badbooger/Enterprise-D-lighting-effects/enterprise documentation/Warp_Core/images/1a5ce3c3165c4e38cc38278a2bccba72_preview_featured.jpg

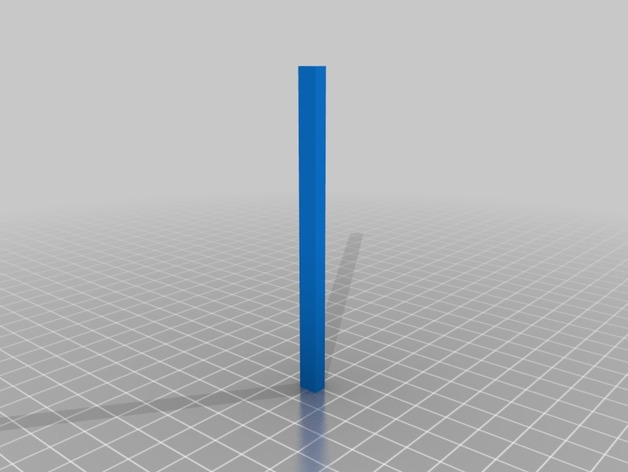
enterprise documentation/Warp_Core/images/1a5ce3c3165c4e38cc38278a2bccba72_preview_featured.jpg
