badbooger/Enterprise-D-lighting-effects/enterprise documentation/Warp_Core/images/2f82c1093543009acfd2d8a2ed61bc1e_preview_featured.jpg

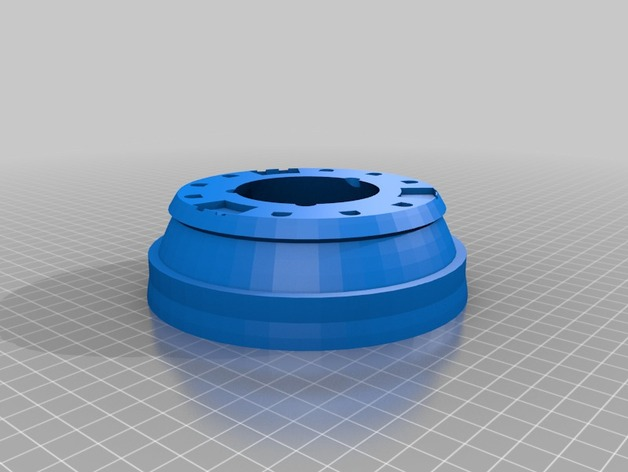
enterprise documentation/Warp_Core/images/2f82c1093543009acfd2d8a2ed61bc1e_preview_featured.jpg
