badbooger/Enterprise-D-lighting-effects/enterprise documentation/Warp_Core/images/4c698710a184a8409cffa17cd85fdf24_preview_featured.jpg

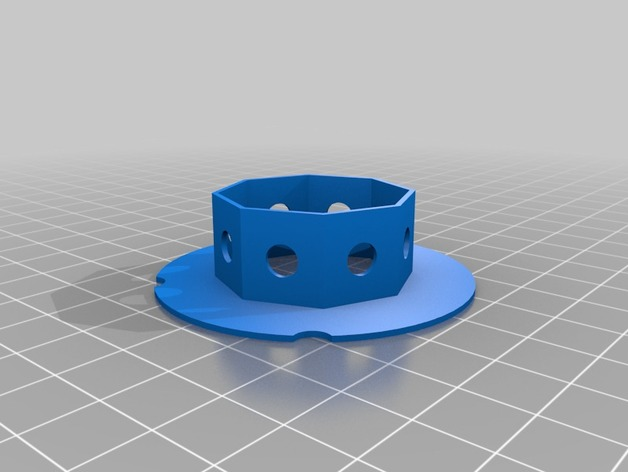
enterprise documentation/Warp_Core/images/4c698710a184a8409cffa17cd85fdf24_preview_featured.jpg
