badbooger/Enterprise-D-lighting-effects/enterprise documentation/Warp_Core/images/5cc91b3e02f9a6b76a1f7cbd91c5c1b0_preview_featured.jpg

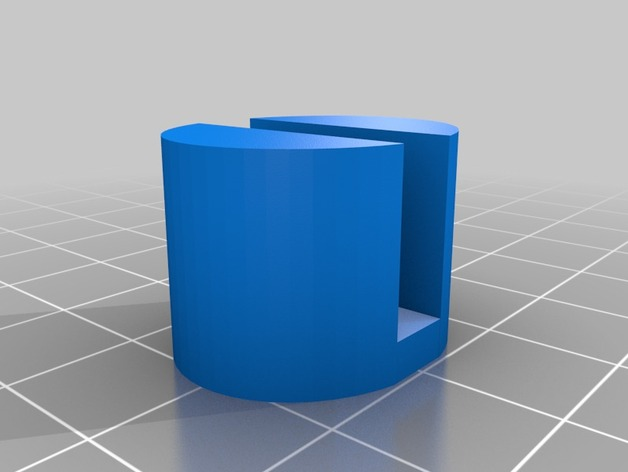
enterprise documentation/Warp_Core/images/5cc91b3e02f9a6b76a1f7cbd91c5c1b0_preview_featured.jpg
