badbooger/Enterprise-D-lighting-effects/enterprise documentation/Warp_Core/images/5dc4bd88d3200d5c8fcbe13b5229334e_preview_featured.jpg

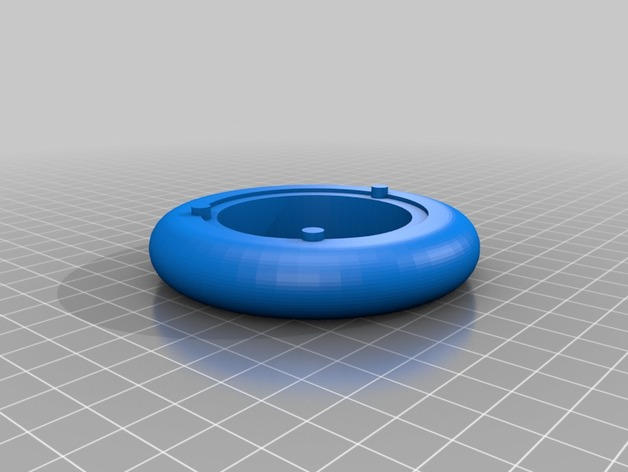
enterprise documentation/Warp_Core/images/5dc4bd88d3200d5c8fcbe13b5229334e_preview_featured.jpg
