badbooger/Enterprise-D-lighting-effects/enterprise documentation/Warp_Core/images/051f70c2b24fe83be3616cc0c08b6ad3_preview_featured.jpg

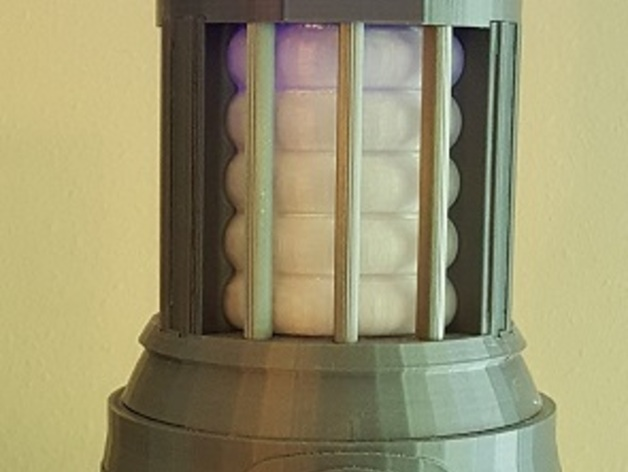
enterprise documentation/Warp_Core/images/051f70c2b24fe83be3616cc0c08b6ad3_preview_featured.jpg
