badbooger/Enterprise-D-lighting-effects/enterprise documentation/Warp_Core/images/58fbbf431e4570eb2abc4635ba671e66_preview_featured.jpg

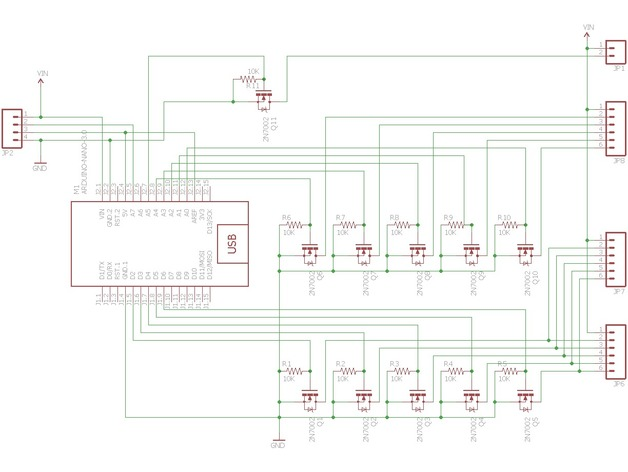
enterprise documentation/Warp_Core/images/58fbbf431e4570eb2abc4635ba671e66_preview_featured.jpg
