badbooger/Enterprise-D-lighting-effects/enterprise documentation/Warp_Core/images/5356e7dd109f7f2495ff2d7921a1a03d_preview_featured.jpg

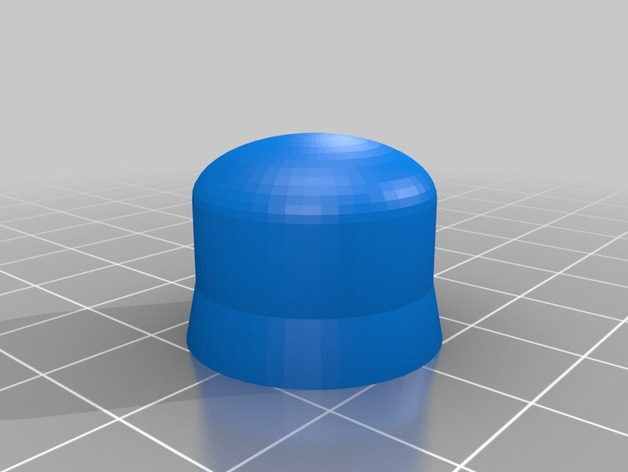
enterprise documentation/Warp_Core/images/5356e7dd109f7f2495ff2d7921a1a03d_preview_featured.jpg
