badbooger/Enterprise-D-lighting-effects/enterprise documentation/Warp_Core/images/6899b61ce81bdb33274d879ba350c7f9_preview_featured.jpg

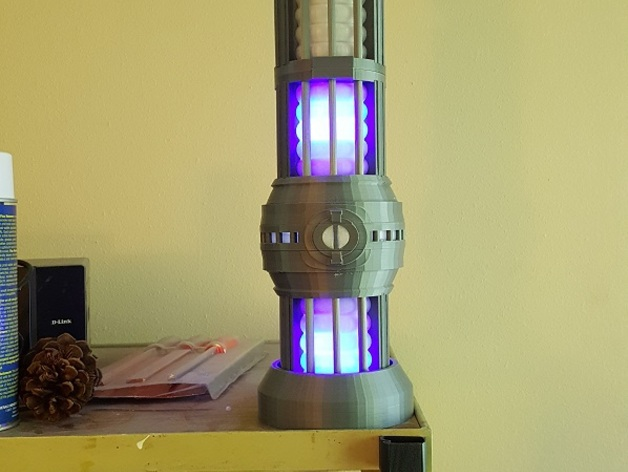
enterprise documentation/Warp_Core/images/6899b61ce81bdb33274d879ba350c7f9_preview_featured.jpg
