badbooger/Enterprise-D-lighting-effects/enterprise documentation/Warp_Core/images/a89cf786b40454a0dcae7b5fe00ec936_preview_featured.jpg

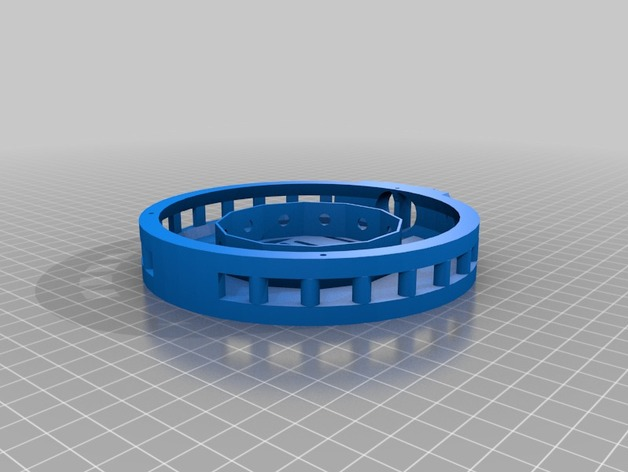
enterprise documentation/Warp_Core/images/a89cf786b40454a0dcae7b5fe00ec936_preview_featured.jpg
