badbooger/Enterprise-D-lighting-effects/red alert.png

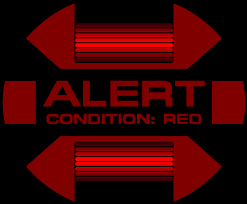
red alert.png
