badbooger/Enterprise-D-lighting-effects/yellow alert.png

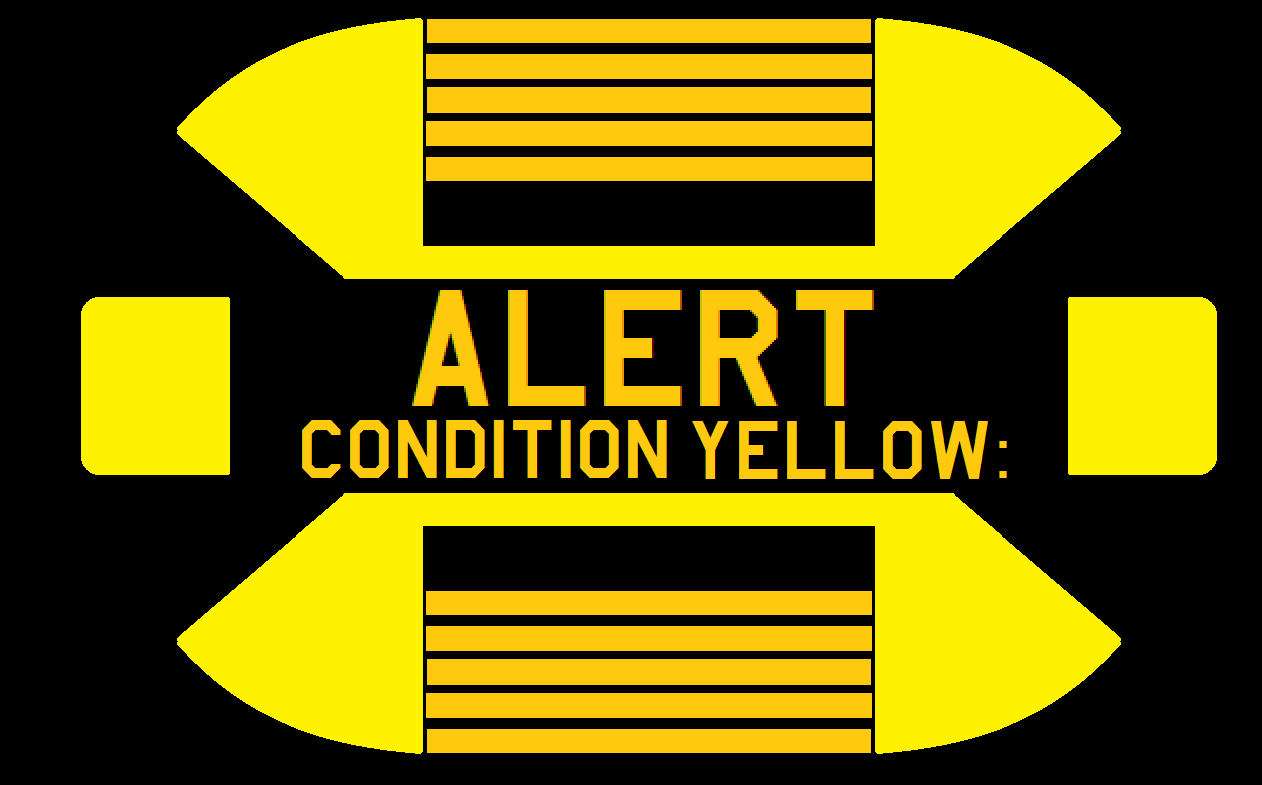
yellow alert.png
