badbooger/Enterprise-D-lighting-effects/enterprise documentation/Warp_Core/files/SupportRingToMI.stl

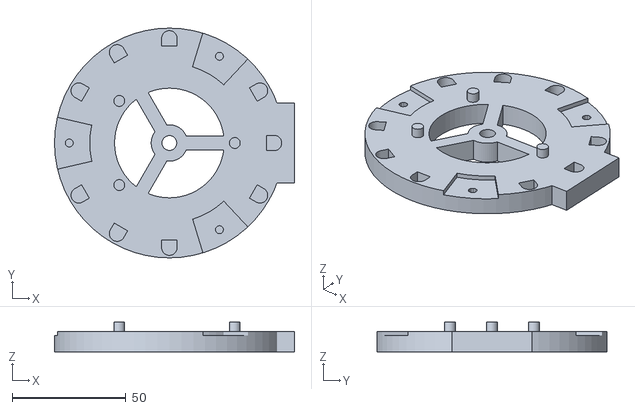
[picture p30: CAD file, 2026-06-05]
enterprise documentation/Warp_Core/files/SupportRingToMI.stl
105.5 x 101.0 x 13.0
