badbooger/Enterprise-D-lighting-effects/enterprise documentation/Warp_Core/files/LightRing.stl

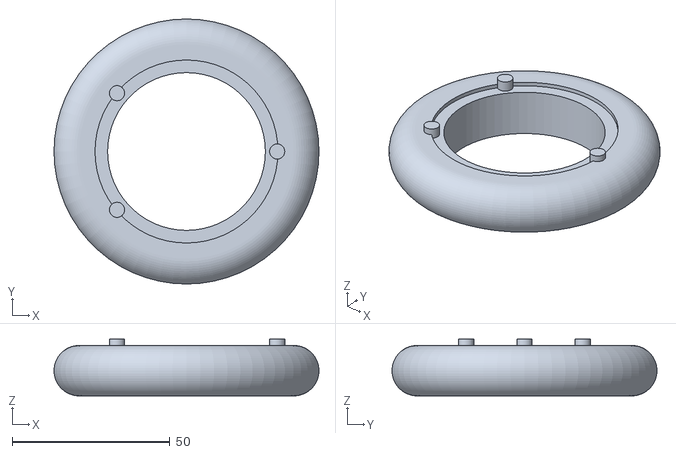
[picture p31: CAD file, 2026-06-05]
enterprise documentation/Warp_Core/files/LightRing.stl
84.0 x 84.0 x 18.0
