badbooger/Enterprise-D-lighting-effects/enterprise documentation/Warp_Core/files/SupportRingBase.stl

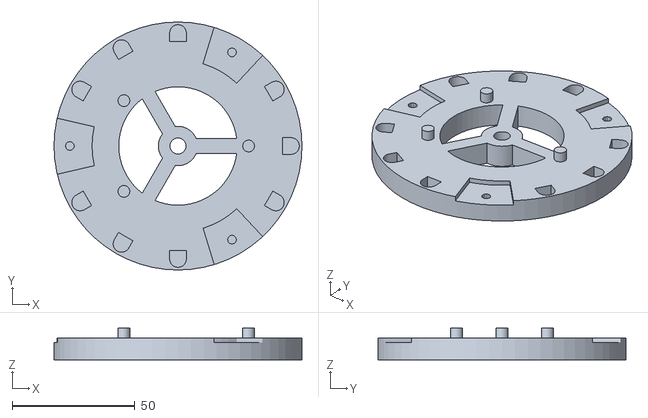
[picture p32: CAD file, 2026-06-05]
enterprise documentation/Warp_Core/files/SupportRingBase.stl
101.0 x 101.0 x 13.0
