badbooger/Enterprise-D-lighting-effects/enterprise documentation/Warp_Core/files/WarpCoreBase.stl

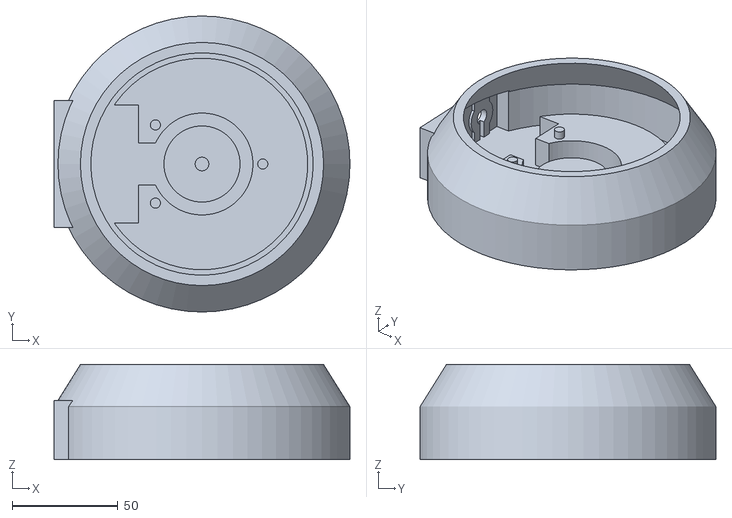
[picture p33: CAD file, 2026-06-05]
enterprise documentation/Warp_Core/files/WarpCoreBase.stl
140.0 x 140.0 x 45.0
