badbooger/Enterprise-D-lighting-effects/enterprise documentation/Warp_Core/files/LightRingSupportUnit.stl

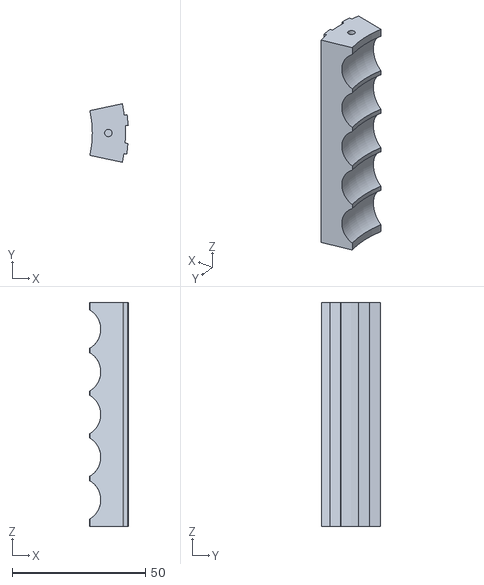
[picture p34: CAD file, 2026-06-05]
enterprise documentation/Warp_Core/files/LightRingSupportUnit.stl
14.4 x 22.0 x 84.0
