badbooger/Enterprise-D-lighting-effects/enterprise documentation/Warp_Core/files/ChamberMiddle.stl

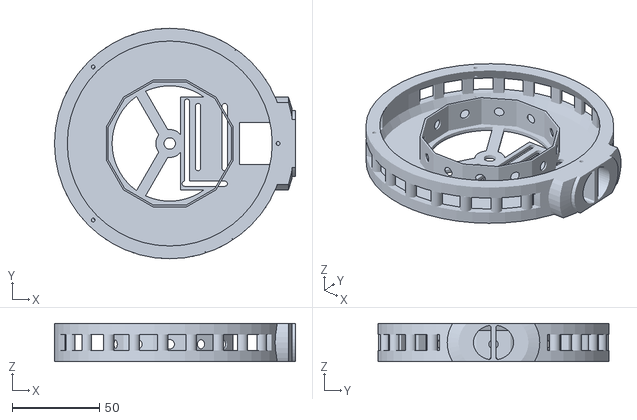
[picture p35: CAD file, 2026-06-05]
enterprise documentation/Warp_Core/files/ChamberMiddle.stl
138.0 x 132.0 x 22.0
