badbooger/Enterprise-D-lighting-effects/enterprise documentation/Warp_Core/files/Upright.stl

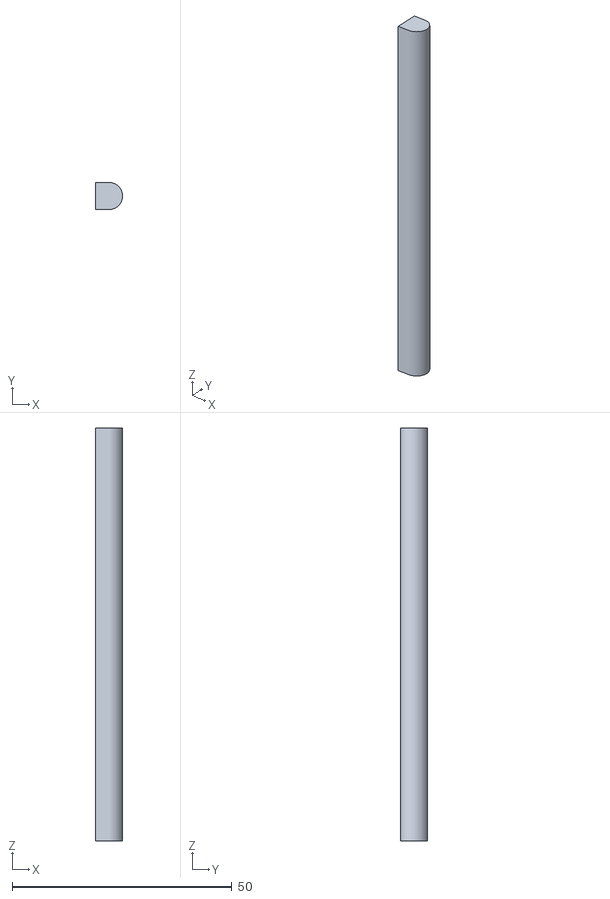
[picture p36: CAD file, 2026-06-05]
enterprise documentation/Warp_Core/files/Upright.stl
6.20 x 6.20 x 94.0
