badbooger/Enterprise-D-lighting-effects/enterprise documentation/Warp_Core/files/MatterInjector_repaired.stl

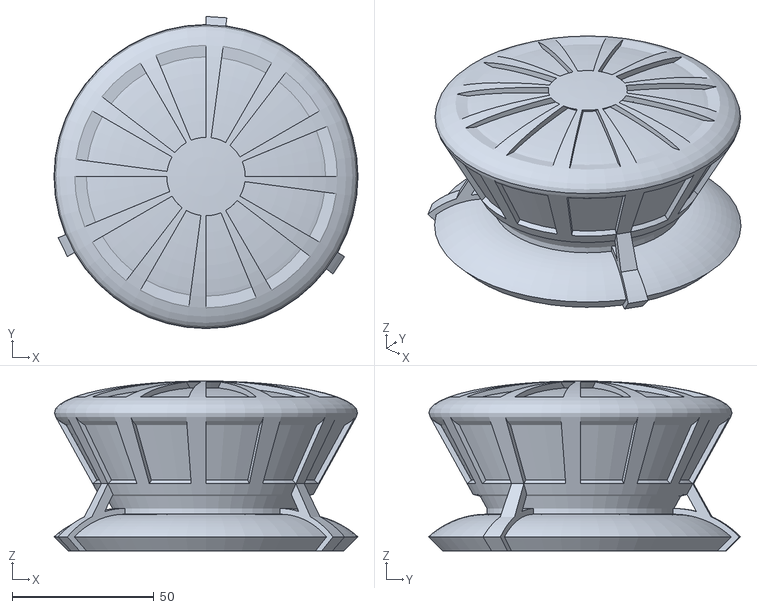
[picture p37: CAD file, 2026-06-05]
enterprise documentation/Warp_Core/files/MatterInjector_repaired.stl
107.3 x 110.2 x 60.0
