badbooger/Enterprise-D-lighting-effects/enterprise documentation/Warp_Core/files/knob.stl

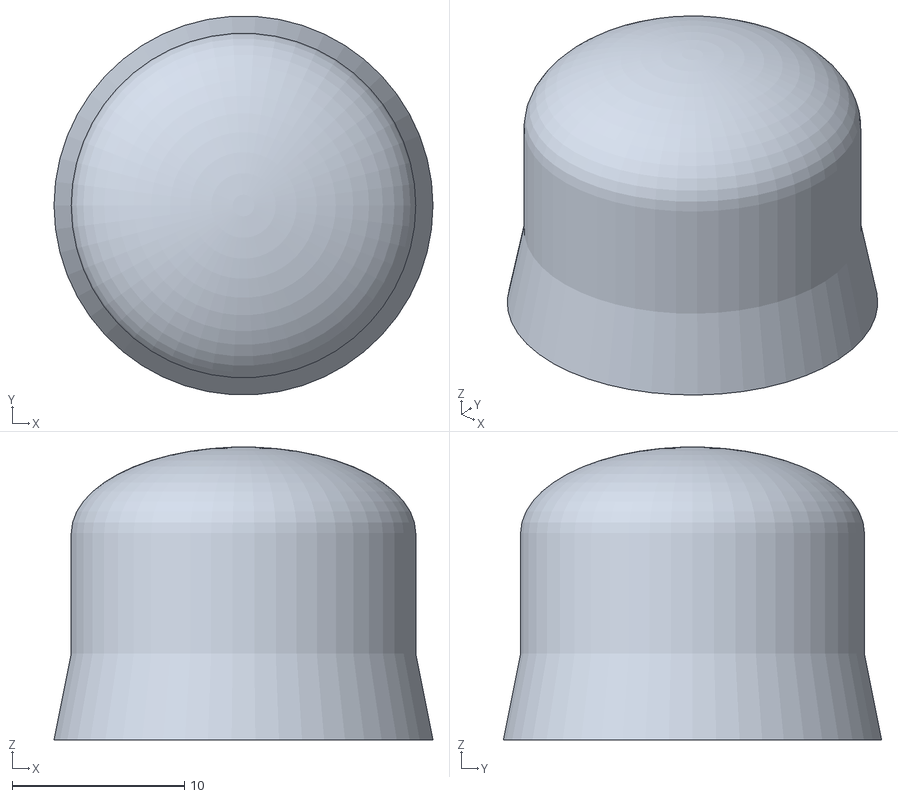
[picture p38: CAD file, 2026-06-05]
enterprise documentation/Warp_Core/files/knob.stl
22.0 x 22.0 x 17.0
