badbooger/Enterprise-D-lighting-effects/Data_Pad/ui_YellowAlert.h

#pragma once

#include "lvgl.h"

#ifdef __cplusplus
extern "C" {
#endif

extern lv_obj_t * ui_YellowAlert;

void ui_YellowAlert_screen_init(void);
void ui_YellowAlert_screen_destroy(void);

#ifdef __cplusplus
}
#endif
